silvianbar/ETTI-2022-2026/P1/Schematics/Orcad/Shema 2 -PSpiceFiles/SCHEMATIC1/AcSweep/AcSweep.cir

** Profile: "SCHEMATIC1-AcSweep"  [ D:\Materii UNIVERSITATE\P1\P1_2024_431D_Baroiu_Silvian_AAF_N6_OrCad\Schematics\Orcad\shema 2 -pspicefiles\schematic1\acsweep.sim ] 

** Creating circuit file "AcSweep.cir" 
** WARNING: THIS AUTOMATICALLY GENERATED FILE MAY BE OVERWRITTEN BY SUBSEQUENT SIMULATIONS

*Libraries: 
* Profile Libraries :
* Local Libraries :
.LIB "D:/Materii UNIVERSITATE/P1/P1_2024_431D_Baroiu_Silvian_AAF_N6_OrCad/Schematics/lib_modelepspice_anexa_1/modele_a1_lib/1n4148."
+ "lib" 
.LIB "D:/Materii UNIVERSITATE/P1/P1_2024_431D_Baroiu_Silvian_AAF_N6_OrCad/Schematics/lib_modelepspice_anexa_1/modele_a1_lib/bc807-2"
+ "5.lib" 
.LIB "D:/Materii UNIVERSITATE/P1/P1_2024_431D_Baroiu_Silvian_AAF_N6_OrCad/Schematics/lib_modelepspice_anexa_1/modele_a1_lib/bc817-2"
+ "5.lib" 
.LIB "D:/Materii UNIVERSITATE/P1/P1_2024_431D_Baroiu_Silvian_AAF_N6_OrCad/Schematics/lib_modelepspice_anexa_1/modele_a1_lib/bc846b."
+ "lib" 
.LIB "D:/Materii UNIVERSITATE/P1/P1_2024_431D_Baroiu_Silvian_AAF_N6_OrCad/Schematics/lib_modelepspice_anexa_1/modele_a1_lib/bc856b."
+ "lib" 
.LIB "D:/Materii UNIVERSITATE/P1/P1_2024_431D_Baroiu_Silvian_AAF_N6_OrCad/Schematics/lib_modelepspice_anexa_1/modele_a1_lib/bzx84c2"
+ "v7.lib" 
.LIB "D:/Materii UNIVERSITATE/P1/P1_2024_431D_Baroiu_Silvian_AAF_N6_OrCad/Schematics/lib_modelepspice_anexa_1/modele_a1_lib/bzx84c5"
+ "v1.lib" 
.LIB "D:/Materii UNIVERSITATE/P1/P1_2024_431D_Baroiu_Silvian_AAF_N6_OrCad/Schematics/lib_modelepspice_anexa_1/modele_a1_lib/bzx84c5"
+ "v6.lib" 
.LIB "D:/Materii UNIVERSITATE/P1/P1_2024_431D_Baroiu_Silvian_AAF_N6_OrCad/Schematics/lib_modelepspice_anexa_1/modele_a1_lib/bzx84c6"
+ "v2.lib" 
.LIB "D:/Materii UNIVERSITATE/P1/P1_2024_431D_Baroiu_Silvian_AAF_N6_OrCad/Schematics/lib_modelepspice_anexa_1/modele_a1_lib/bzx84c6"
+ "v8.lib" 
.LIB "D:/Materii UNIVERSITATE/P1/P1_2024_431D_Baroiu_Silvian_AAF_N6_OrCad/Schematics/lib_modelepspice_anexa_1/modele_a1_lib/bzx84c8"
+ "v2.lib" 
.LIB "D:/Materii UNIVERSITATE/P1/P1_2024_431D_Baroiu_Silvian_AAF_N6_OrCad/Schematics/lib_modelepspice_anexa_1/modele_a1_lib/bzx84c1"
+ "0.lib" 
.LIB "D:/Materii UNIVERSITATE/P1/P1_2024_431D_Baroiu_Silvian_AAF_N6_OrCad/Schematics/lib_modelepspice_anexa_1/modele_a1_lib/irfr120"
+ "npbf.lib" 
.LIB "D:/Materii UNIVERSITATE/P1/P1_2024_431D_Baroiu_Silvian_AAF_N6_OrCad/Schematics/lib_modelepspice_anexa_1/modele_a1_lib/mjd31cg"
+ ".lib" 
.LIB "D:/Materii UNIVERSITATE/P1/P1_2024_431D_Baroiu_Silvian_AAF_N6_OrCad/Schematics/lib_modelepspice_anexa_1/modele_a1_lib/mjd32cg"
+ ".lib" 
.LIB "D:/Materii UNIVERSITATE/P1/P1_2024_431D_Baroiu_Silvian_AAF_N6_OrCad/Schematics/lib_modelepspice_anexa_1/modele_a1_lib/mmbfj17"
+ "7lt1g.lib" 
.LIB "D:/Materii UNIVERSITATE/P1/P1_2024_431D_Baroiu_Silvian_AAF_N6_OrCad/Schematics/lib_modelepspice_anexa_1/modele_a1_lib/mmbfj30"
+ "9lt1g.lib" 
* From [PSPICE NETLIST] section of C:\Users\silvi\AppData\Roaming\SPB_Data\cdssetup\OrCAD_PSpice\17.2.0\PSpice.ini file:
.lib "nomd.lib" 

*Analysis directives: 
.AC DEC 100 0.001 10Meg
.OPTIONS ADVCONV
.PROBE64 V(alias(*)) I(alias(*)) W(alias(*)) D(alias(*)) NOISE(alias(*)) 
.INC "..\SCHEMATIC1.net" 


.END
