silvianbar/ETTI-2022-2026/P1/Schematics/Orcad/Shema 2 -PSpiceFiles/SCHEMATIC1/bias/bias.cir

** Profile: "SCHEMATIC1-bias"  [ d:\materii universitate\p1\proiecte\shema 2 -pspicefiles\schematic1\bias.sim ] 

** Creating circuit file "bias.cir" 
** WARNING: THIS AUTOMATICALLY GENERATED FILE MAY BE OVERWRITTEN BY SUBSEQUENT SIMULATIONS

*Libraries: 
* Profile Libraries :
* Local Libraries :
.LIB "d:/materii universitate/p1/lib_modelepspice_anexa_1/modele_a1_lib/1n4148.lib" 
.LIB "d:/materii universitate/p1/lib_modelepspice_anexa_1/modele_a1_lib/bc807-25.lib" 
.LIB "d:/materii universitate/p1/lib_modelepspice_anexa_1/modele_a1_lib/bc817-25.lib" 
.LIB "d:/materii universitate/p1/lib_modelepspice_anexa_1/modele_a1_lib/bc846b.lib" 
.LIB "d:/materii universitate/p1/lib_modelepspice_anexa_1/modele_a1_lib/bc856b.lib" 
.LIB "d:/materii universitate/p1/lib_modelepspice_anexa_1/modele_a1_lib/bzx84c2v7.lib" 
.LIB "d:/materii universitate/p1/lib_modelepspice_anexa_1/modele_a1_lib/bzx84c5v1.lib" 
.LIB "d:/materii universitate/p1/lib_modelepspice_anexa_1/modele_a1_lib/bzx84c5v6.lib" 
.LIB "d:/materii universitate/p1/lib_modelepspice_anexa_1/modele_a1_lib/bzx84c6v2.lib" 
.LIB "d:/materii universitate/p1/lib_modelepspice_anexa_1/modele_a1_lib/bzx84c6v8.lib" 
.LIB "d:/materii universitate/p1/lib_modelepspice_anexa_1/modele_a1_lib/bzx84c8v2.lib" 
.LIB "d:/materii universitate/p1/lib_modelepspice_anexa_1/modele_a1_lib/bzx84c10.lib" 
.LIB "d:/materii universitate/p1/lib_modelepspice_anexa_1/modele_a1_lib/irfr120npbf.lib" 
.LIB "d:/materii universitate/p1/lib_modelepspice_anexa_1/modele_a1_lib/mjd31cg.lib" 
.LIB "d:/materii universitate/p1/lib_modelepspice_anexa_1/modele_a1_lib/mjd32cg.lib" 
.LIB "d:/materii universitate/p1/lib_modelepspice_anexa_1/modele_a1_lib/mmbfj177lt1g.lib" 
.LIB "d:/materii universitate/p1/lib_modelepspice_anexa_1/modele_a1_lib/mmbfj309lt1g.lib" 
* From [PSPICE NETLIST] section of C:\Users\silvi\AppData\Roaming\SPB_Data\cdssetup\OrCAD_PSpice\17.2.0\PSpice.ini file:
.lib "nomd.lib" 

*Analysis directives: 
.TRAN  0 10ms 0 0.001ms 
.OPTIONS ADVCONV
.PROBE64 V(alias(*)) I(alias(*)) W(alias(*)) D(alias(*)) NOISE(alias(*)) 
.INC "..\SCHEMATIC1.net" 


.END
